openreed/cane-splitter/docs/images/bassoon/body_bottom.png

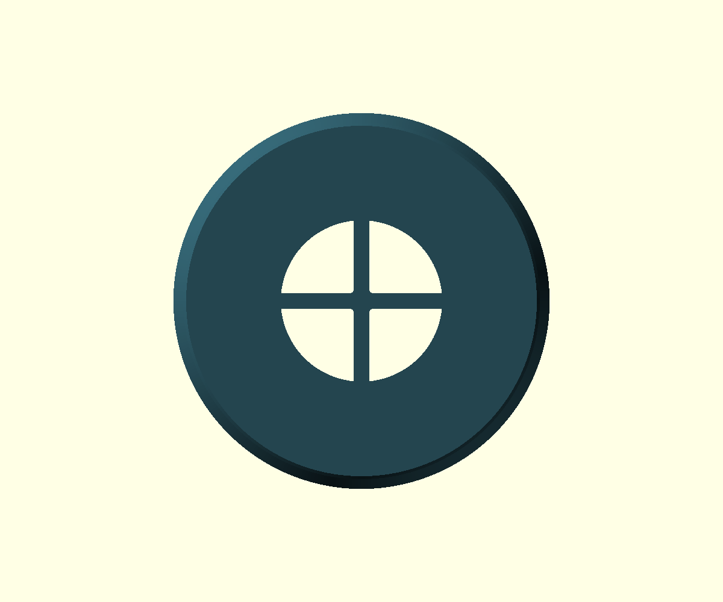
docs/images/bassoon/body_bottom.png
