openreed/cane-splitter/docs/images/bassoon/exploded.png

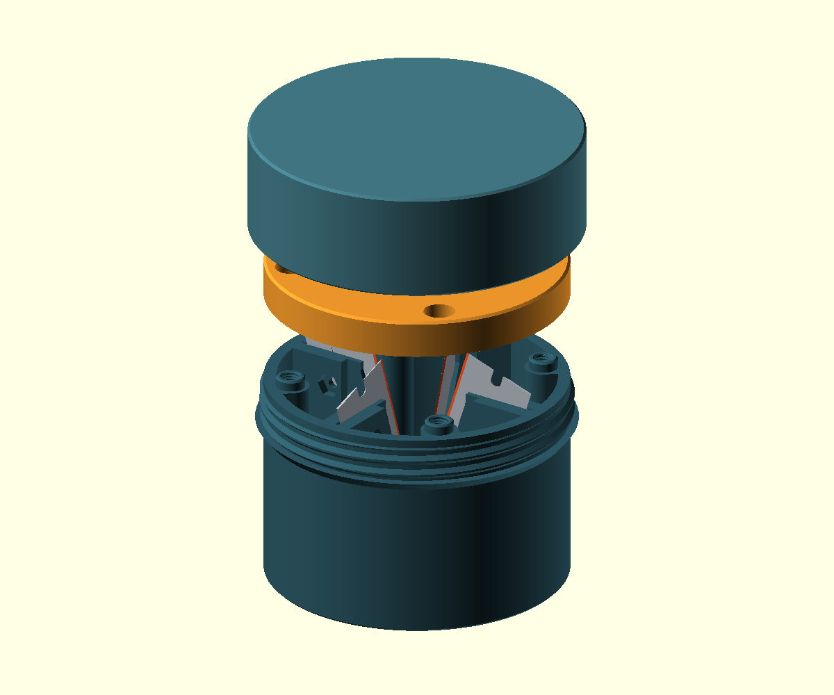
docs/images/bassoon/exploded.png
