openreed/cane-splitter/docs/images/bassoon/locking_ring.png

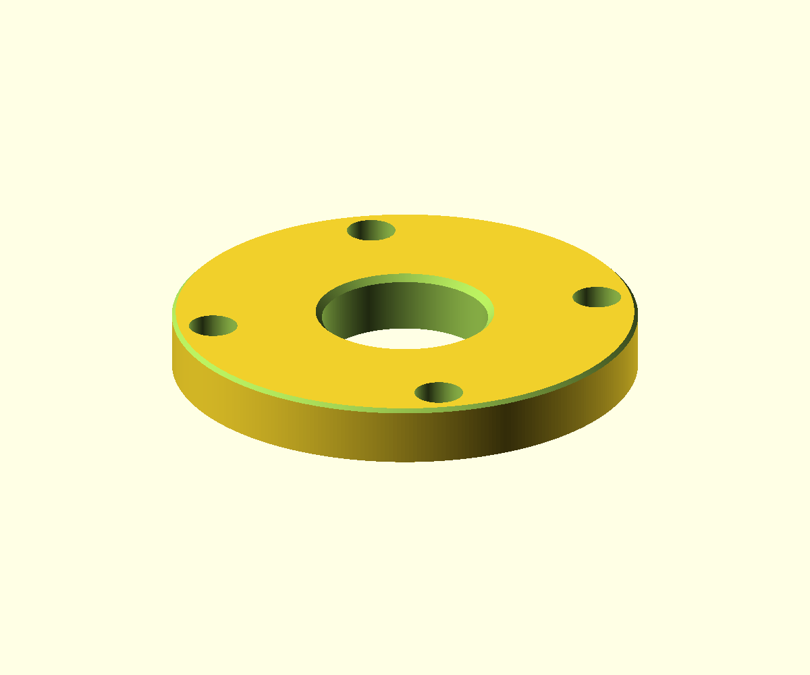
docs/images/bassoon/locking_ring.png
