openreed/cane-splitter/docs/images/bassoon/root_detail.png

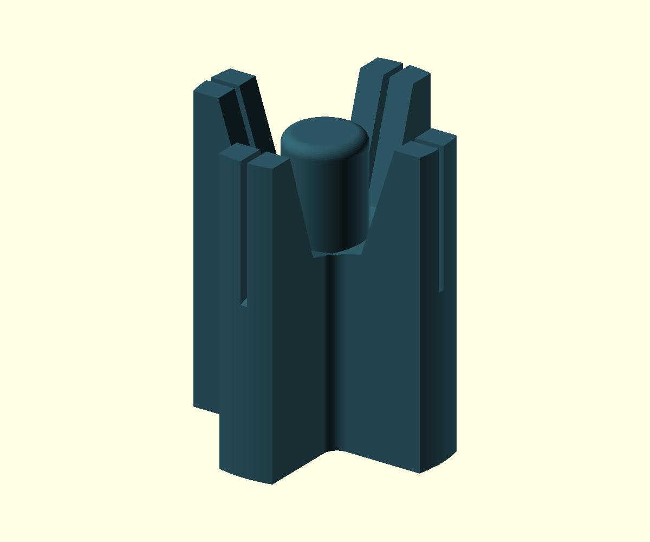
docs/images/bassoon/root_detail.png
