openreed/cane-splitter/docs/images/bassoon/section.png

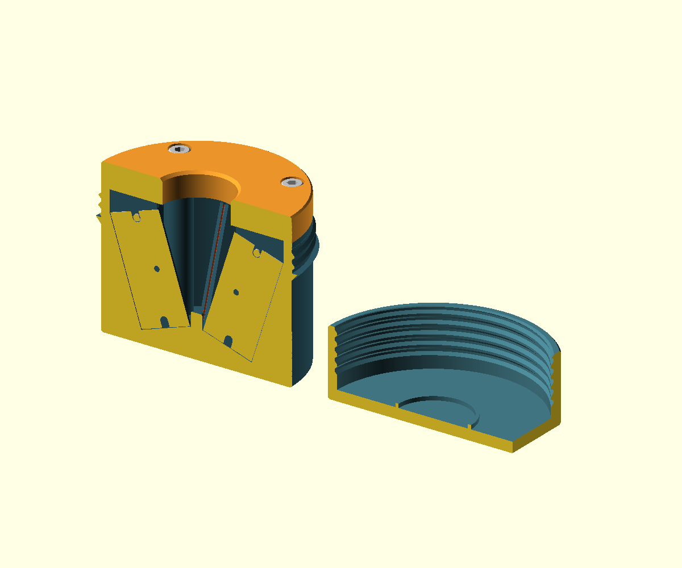
docs/images/bassoon/section.png
