openreed/cane-splitter/docs/images/oboe/locking_ring_bottom.png

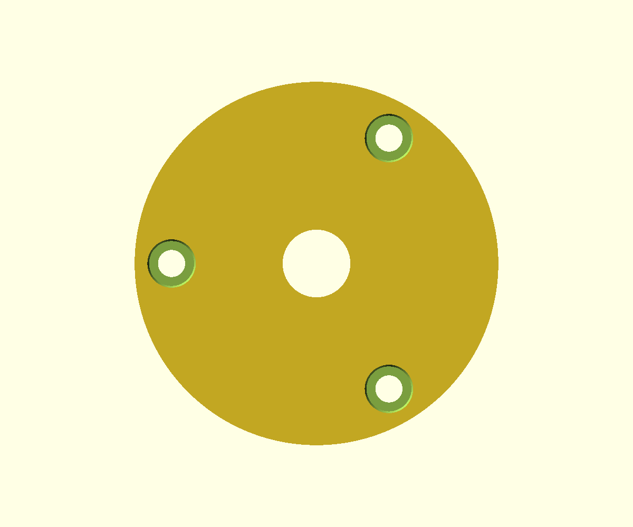
docs/images/oboe/locking_ring_bottom.png
