openreed/cane-splitter/docs/images/oboe/palm_cap.png

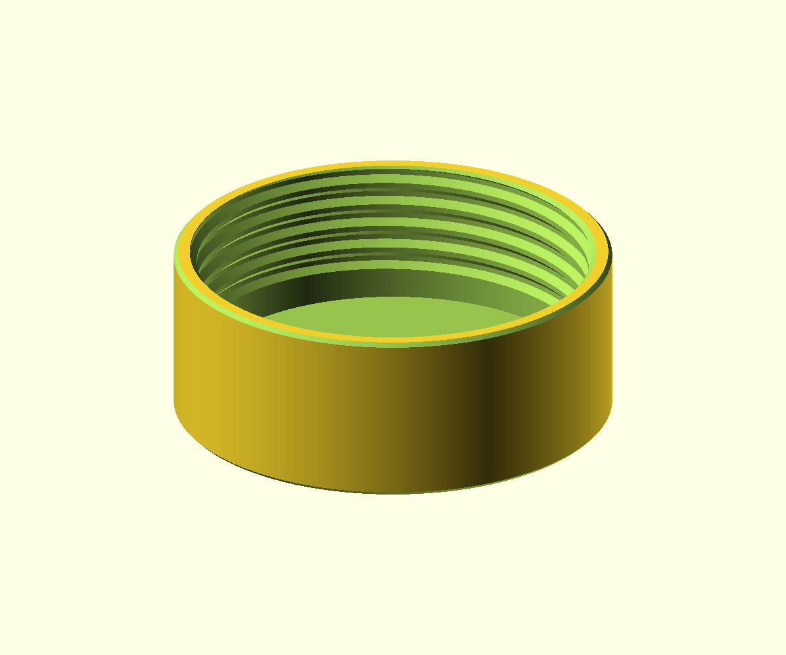
docs/images/oboe/palm_cap.png
