openreed/cane-splitter/docs/images/bassoon/assembly.png

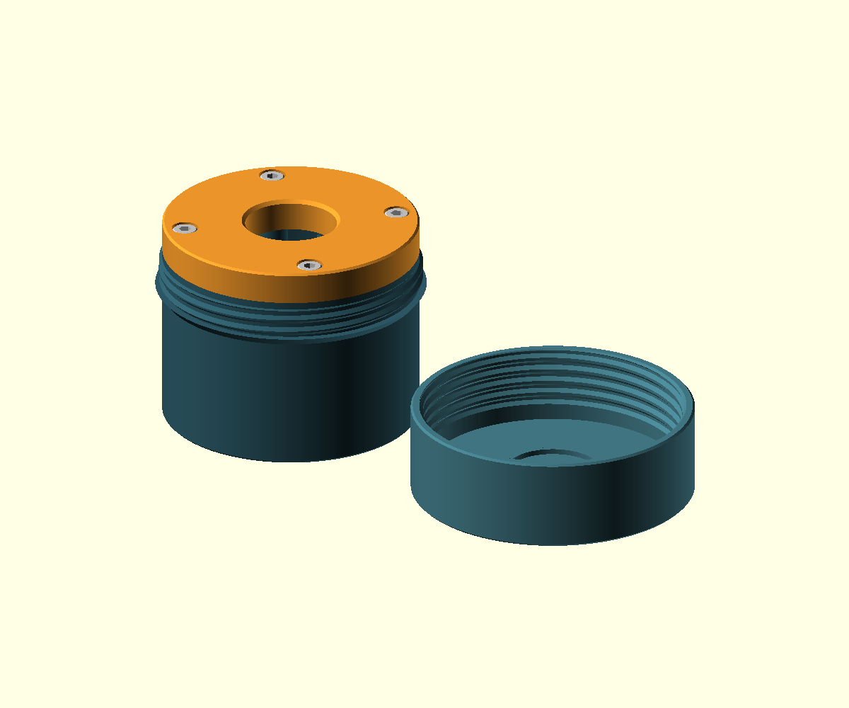
docs/images/bassoon/assembly.png
